wa1hco/Tiny_Sequencer_Hardware/Key_Input_LTspice_Model.asc

D1: zener; MYD
R1: res; 510
R2: res; 2.2K
R3: res; 20K
U1: PC817A
V1: voltage; PULSE(0 20 0 1 0 0 0 1)
V2: voltage; 3.3
Named nets: 0, Vmcu, Vin, Vz, Vled
.tran 0 1 0
.model MYD ako: BZX84B8V2L Bv=3.6
